FPGA-Computer/Battery-Analyzer/Ver 2.1 Rel 0/LTSpice/buckboost.asc

C1: cap; 1µ
C2: cap; 22p
C3: cap; .1µ
C4: cap; 1µ; V=10 Irms=0 Rser=0.009 Lser=0 mfg="TDK" pn="C1608X5RIA105K" type="X5R"
D1: schottky; MBRS140
L1: ind; 22µ; Ipk=0.5 Rser=0.81 Rpar=0 Cpar=0 mfg="Murata" pn="LQH32PN220MN0"
L2: ind; 22µ; Ipk=0.5 Rser=0.81 Rpar=0 Cpar=0 mfg="Murata" pn="LQH32PN220MN0"
R1: res; 39.2k
R2: res; 13k
R3: res; 10K
Rload: res; 40
U1: LT3460
V1: VOLTAGE; 4
Named nets: 0, OUT, IN
.tran 2ms startup
