FPGA-Computer/Battery-Analyzer/Ver 2.1 Rel 0/LTSpice/current sense -1.asc

R6: res; 0.25R
R8: res; 1K
R10: res; 4k75
V4: voltage; PULSE(-0.5V 0.5V 1ms 10ms); Rser=0.1r
V5: voltage; 3.3V
Named nets: 0
.include "NTD20N03L27.REV0.SP3"
.include "LM2903.lib"
.include "LM2904.lib"
.tran 20ms
