FPGA-Computer/Battery-Analyzer/Ver 2.1 Rel 0/LTSpice/PWM filter-1.asc

C1: cap; 1µ; V=10 Irms=0 Rser=0.009 Lser=0 mfg="TDK" pn="C1608X5RIA105K" type="X5R"
C2: cap; 0.1µF; V=10 Irms=0 Rser=0.009 Lser=0
C3: cap; 0.1µF
R1: res; 1K
R2: res; 10K
R3: res; 10K
V1: voltage; PULSE(0V 3.3V 0 5ns 5ns 334us 668us); Rser=60R
Named nets: 0, RC1, RC2, RC3
.tran 0 50ms 0
