FPGA-Computer/Battery-Analyzer/Ver 2.1 Rel 0/LTSpice/saw tooth-discrete.asc

C1: cap; 22pF
C2: cap; 1nF
C3: cap; 0.1µF
Q1: pnp; 2N3906
R1: res; 39K
R2: res; 475R
R3: res; 10K
R4: res; 1K2
R5: res; 4K7
U2: opamp2; lm2903
V1: voltage; 5V
V2: voltage; 3.3V
Named nets: 0, Vout
.include "LM2903.lib"
.tran 500us startup
