FPGA-Computer/Battery-Analyzer/Ver 2.1 Rel 0/LTSpice/soft start.asc

C1: cap; 0.1µF
C2: polcap; 470µ; V=25 Irms=1.01 Rser=0.065 Lser=0 mfg="Panasonic" pn="ECA1EFQ471" type="Al electrolytic"
C3: polcap; 470µ; V=25 Irms=1.01 Rser=0.065 Lser=0 mfg="Panasonic" pn="ECA1EFQ471" type="Al electrolytic"
M1: pmos; ""
Q1: pnp; 2N3906
R1: res; 100K
R2: res; 1K
R3: res; 100R
V1: voltage; PULSE(0 5V 1ms 100ns); Rser=0.1R
V2: voltage; PULSE(0 5V 1ms 100ns); Rser=0.1R
Named nets: 0
.include "Si2307bd.lib"
.tran 120ms startup
