FPGA-Computer/Battery-Analyzer/Windows/charger21/pcb.h

/*
 * pcb.h
 *
 * Created: 20/07/2013 2:26:06 PM
 *  Author: K. C. Lee
 * Copyright (c) 2015 by K. C. Lee
 *
 * The software is under Mozilla Public License
 * The full detail of this license is available at: 
 * https://www.mozilla.org/MPL/
 */ 


#ifndef PCB_H_
#define PCB_H_

#define BAUD		115200L

#define BIG_ENDIAN              1
#define USB_VENDOR_NAME		'F','P','G','A','-','C','o','m','p','u','t','e','r'
#define USB_VENDOR_NAME_LEN	13
#define USB_DEVICE_NAME		'R','a','i','d','e','n'
#define USB_DEVICE_NAME_LEN	6
#define USB_SERIAL_NUMBER	'0','0','0','0','0','0'
#define USB_SERIAL_NUMBER_LEN   6

#define USB_INTR_POLL_INTERVAL	10

#define CHARGERS		2
#endif /* PCB_H_ */
